Delaune-Remi/Station_Meteo/Analyse_Fonctionnelle/DefinitionBlocs.PNG

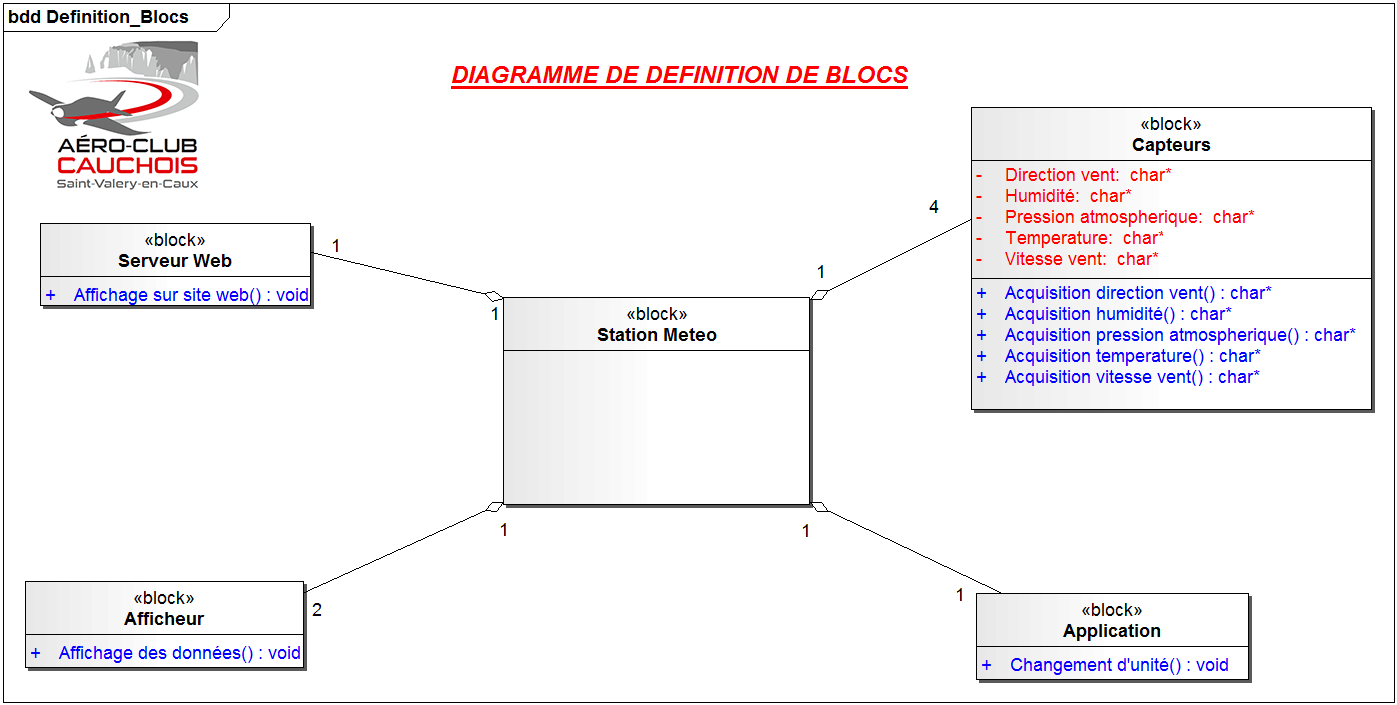
Analyse_Fonctionnelle/DefinitionBlocs.PNG
