Delaune-Remi/Station_Meteo/Analyse_Fonctionnelle/Sequence.png

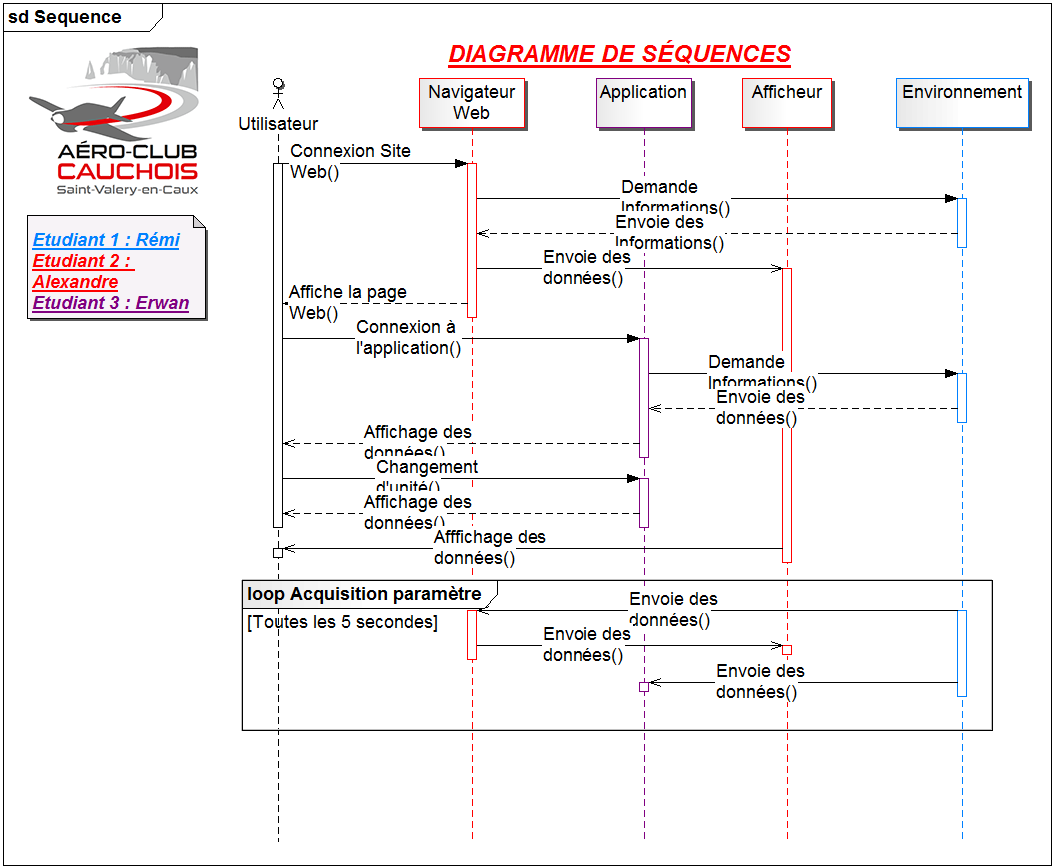
Analyse_Fonctionnelle/Sequence.png
