Delaune-Remi/Station_Meteo/Documentation/Station_meteo_aeroclub/HIH8120.jpg

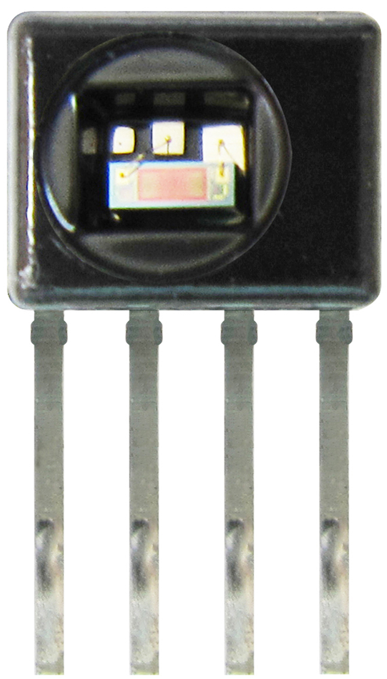
Documentation/Station_meteo_aeroclub/HIH8120.jpg
