Delaune-Remi/Station_Meteo/Documentation/Station_meteo_aeroclub/Pression altitude.png

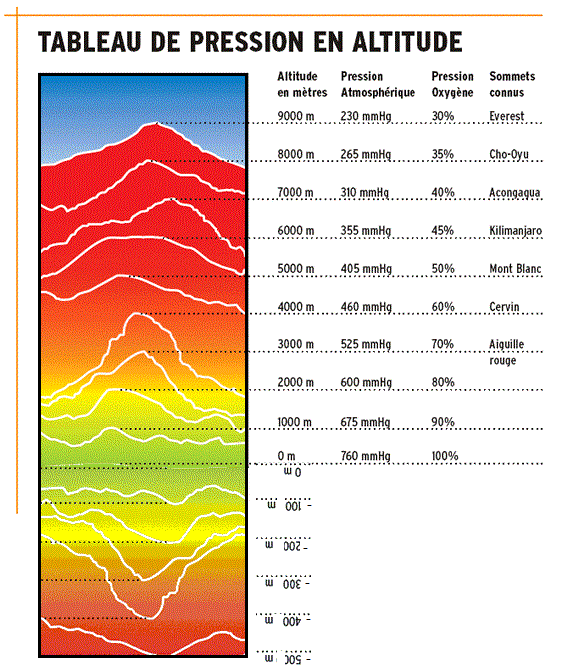
Documentation/Station_meteo_aeroclub/Pression altitude.png
