Delaune-Remi/Station_Meteo/Partie_Alexandre/Image/dessin-de-rose-des-vents.jpg

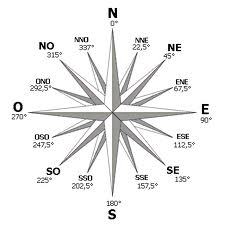
Partie_Alexandre/Image/dessin-de-rose-des-vents.jpg
