Delaune-Remi/Station_Meteo/Partie_Alexandre/Image/Schema_Densemble.PNG

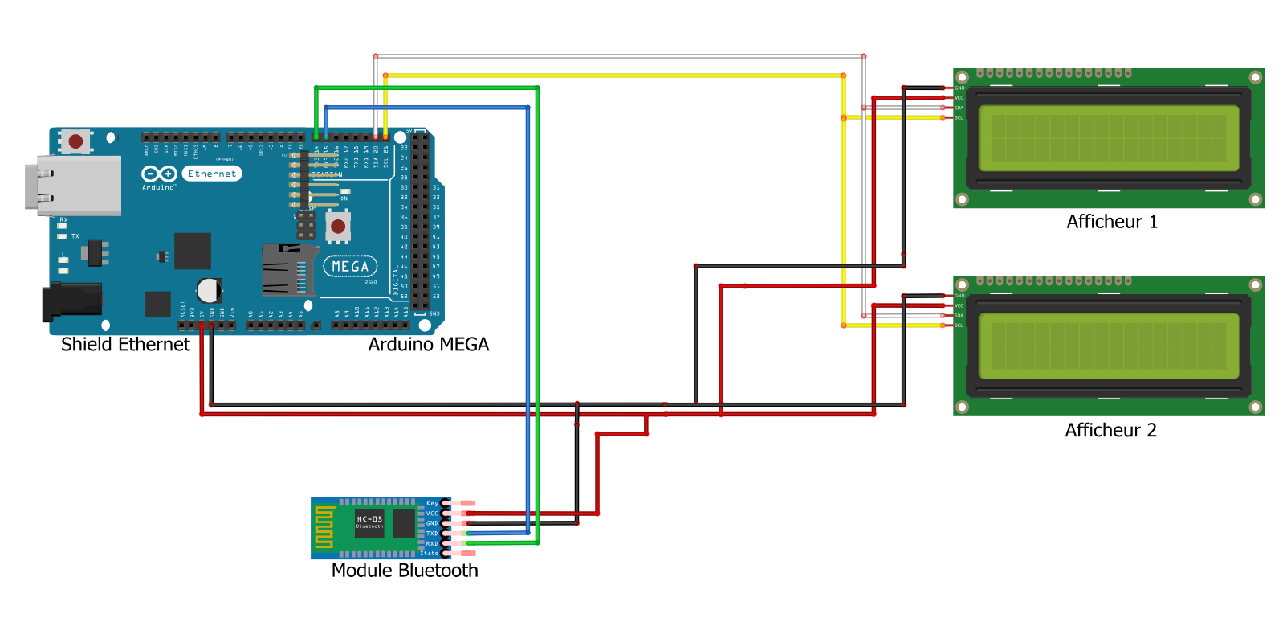
Partie_Alexandre/Image/Schema_Densemble.PNG
