Delaune-Remi/Station_Meteo/Partie_Alexandre/Image/Vuecarte.png

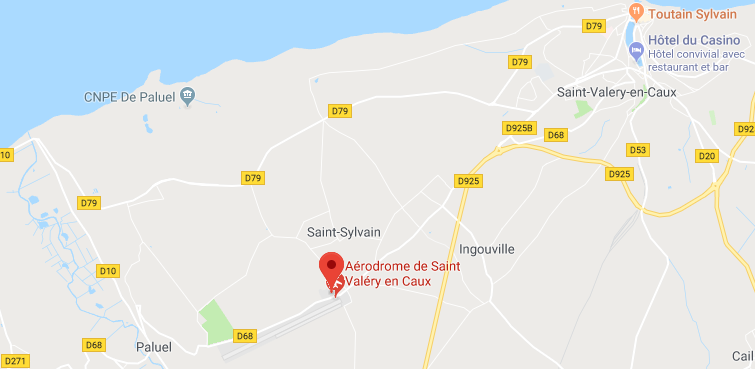
Partie_Alexandre/Image/Vuecarte.png
