Delaune-Remi/Station_Meteo/Partie_Remi/Images/IMAGE PROJET/20180205_113102.jpg

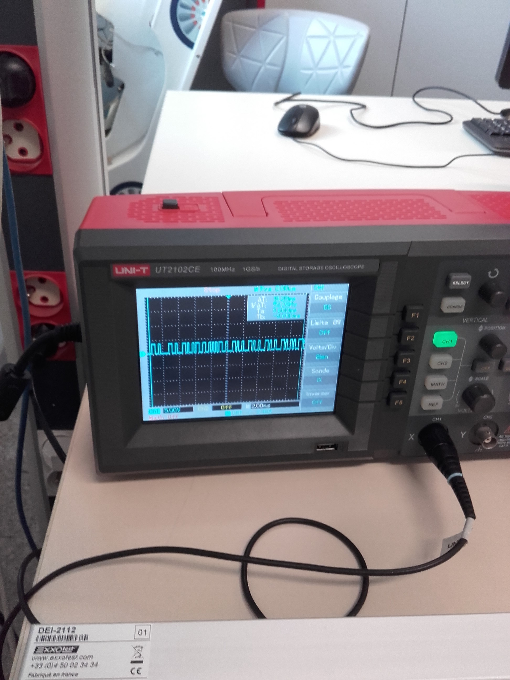
Partie_Remi/Images/IMAGE PROJET/20180205_113102.jpg
