Delaune-Remi/Station_Meteo/Partie_Remi/Images/IMAGE PROJET/20180419_111539.jpg

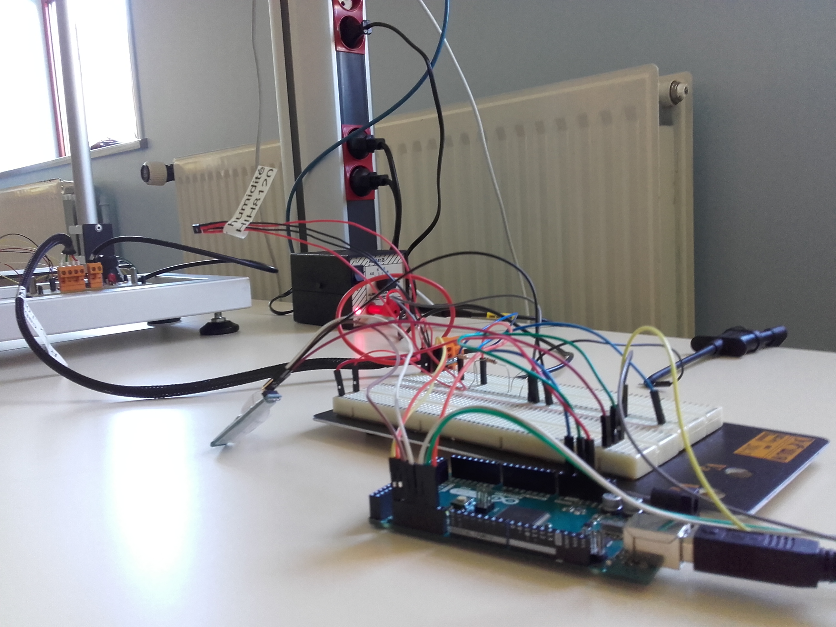
Partie_Remi/Images/IMAGE PROJET/20180419_111539.jpg
