Delaune-Remi/Station_Meteo/Partie_Remi/Images/IMAGE PROJET/20180419_111733.jpg

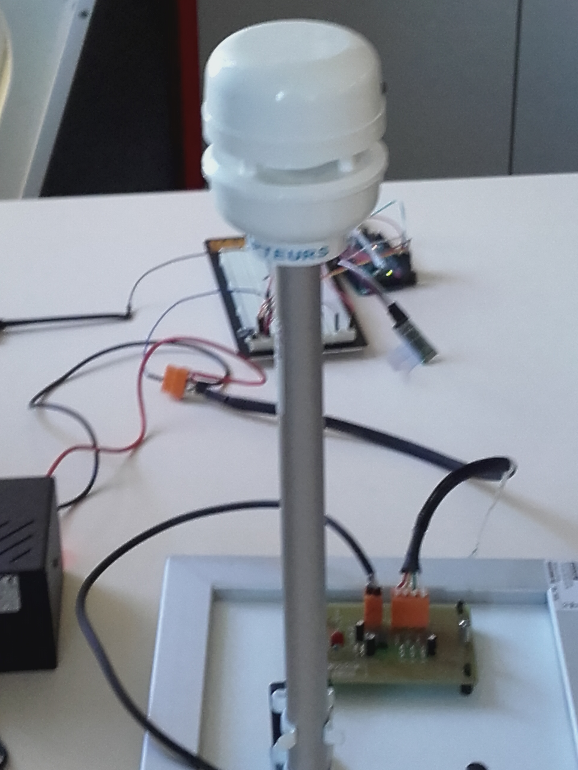
Partie_Remi/Images/IMAGE PROJET/20180419_111733.jpg
