Delaune-Remi/Station_Meteo/Partie_Alexandre/Programme_Final/Inimeac.cpp

#include "Inimeac.h"

Inimeac::Inimeac(){
	this->m_Trame=new char [104];
  
}

Inimeac::~Inimeac(){
	delete (m_Trame);
}

char Inimeac::setTrame (const char* VitesseVent,const char* DirectionVent,const char* Temperature,const char* Hygrometrie, const char* Pression, const char* Validite){
	strcpy (this->m_Trame,"&#!INIMEAC");
	strcat (this->m_Trame,";!SWD::");
	strcat (this->m_Trame,VitesseVent);
	strcat (this->m_Trame,"::KTS");
	strcat (this->m_Trame,";!DWD::");
	strcat (this->m_Trame,DirectionVent);
	strcat (this->m_Trame,"::D");
	strcat (this->m_Trame,";!TMP::");
	strcat (this->m_Trame,Temperature);
	strcat (this->m_Trame,"::C");
	strcat (this->m_Trame,";!RHY::");
	strcat (this->m_Trame,Hygrometrie);
	strcat (this->m_Trame,"::%");
	strcat (this->m_Trame,";!RPA::");
	strcat (this->m_Trame,Pression);
	strcat (this->m_Trame,"::hPa");
	strcat (this->m_Trame,";!VAD::");
	strcat (this->m_Trame,Validite);
	strcat (this->m_Trame,":!");
	if (Validite == "Y"){
		return 'V';
	}else{
		return 'E';
	}
}

char* Inimeac::getTrame (){
	return (this->m_Trame);
}

char Inimeac::decodeTrameINIMEAC(String m_TrameDecode,bool trameComplete,char* const VitesseVent, char* const DirectionVent, char* const Temperature, char* const Hygrometrie,char* const Pression){
  
  
  if (trameComplete==true) { 
      
      VitesseVent[0]= m_TrameDecode[17];
      VitesseVent[1]= m_TrameDecode[18];
      VitesseVent[2]= m_TrameDecode[19];
      VitesseVent[3]= m_TrameDecode[20];
      VitesseVent[4]= m_TrameDecode[21];
      VitesseVent[5]= m_TrameDecode[22];

      DirectionVent[0]= m_TrameDecode[35];
      DirectionVent[1]= m_TrameDecode[36];
      DirectionVent[2]= m_TrameDecode[37];
      DirectionVent[3]= m_TrameDecode[38];
      DirectionVent[4]= m_TrameDecode[39];

      Temperature[0]= m_TrameDecode[50];
      Temperature[1]= m_TrameDecode[51];
      Temperature[2]= m_TrameDecode[52];
      Temperature[3]= m_TrameDecode[53];
      Temperature[4]= m_TrameDecode[54];
    
      Hygrometrie[1]= m_TrameDecode[65];
      Hygrometrie[2]= m_TrameDecode[66];
      Hygrometrie[3]= m_TrameDecode[67];
      Hygrometrie[4]= m_TrameDecode[68];
      Hygrometrie[5]= m_TrameDecode[69];
      Hygrometrie[6]= m_TrameDecode[70];
      
      Pression[0]= m_TrameDecode[80];
      Pression[1]= m_TrameDecode[81];
      Pression[2]= m_TrameDecode[82];
      Pression[3]= m_TrameDecode[83];
      Pression[4]= m_TrameDecode[84];
      Pression[5]= m_TrameDecode[85];
      Pression[6]= m_TrameDecode[86];
      Pression[7]= m_TrameDecode[87];
  } 
}

/*
Exemple de Trame INIMEAC:

&#!INIMEAC;!SWD::000.00::KTS;!DWD::000.0::D;!TMP::00.00::C;!RHY::000.00::%;!RPA::1013.25::hPa;!VAD::N:!

*/
